fredriknk/spimux/CAD/Relay_group.kicad_sch

## KiCad design CAD/Relay_group.kicad_sch (2023-02-07)

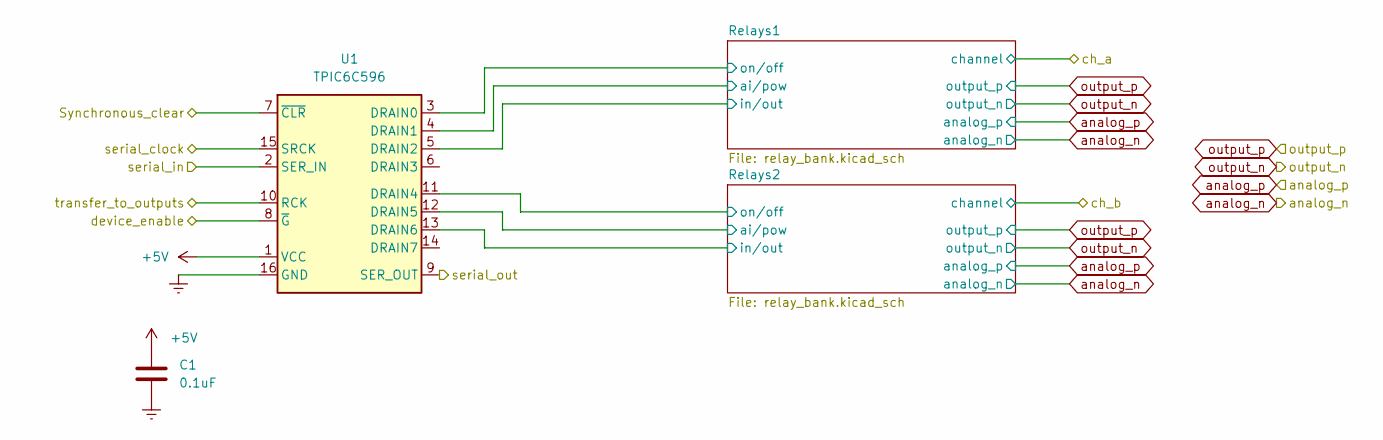
[picture p32: schematic Relay_group.kicad_sch]

Parts:
C1: 0.1uF; D_0603_1608Metric; Digikey CL10B104KB8NFNC
U1: TPIC6C596; TSSOP-16_4.4x5mm_P0.65mm; Digikey TPIC6C596PWR

Connections:
+5V: C1.1, U1.1 (VCC)
Earth: C1.2, U1.16 (GND)
Synchronous_clear: U1.7 (~CLR)
ai/pow: U1.4 (DRAIN1), U1.12 (DRAIN5)
device_enable: U1.8 (~G)
in/out: U1.5 (DRAIN2), U1.13 (DRAIN6)
on/off: U1.3 (DRAIN0), U1.11 (DRAIN4)
serial_clock: U1.15 (SRCK)
serial_in: U1.2 (SER_IN)
serial_out: U1.9 (SER_OUT)
transfer_to_outputs: U1.10 (RCK)
