fredriknk/spimux/CAD/buffer.kicad_sch

## KiCad design CAD/buffer.kicad_sch (2023-02-07)

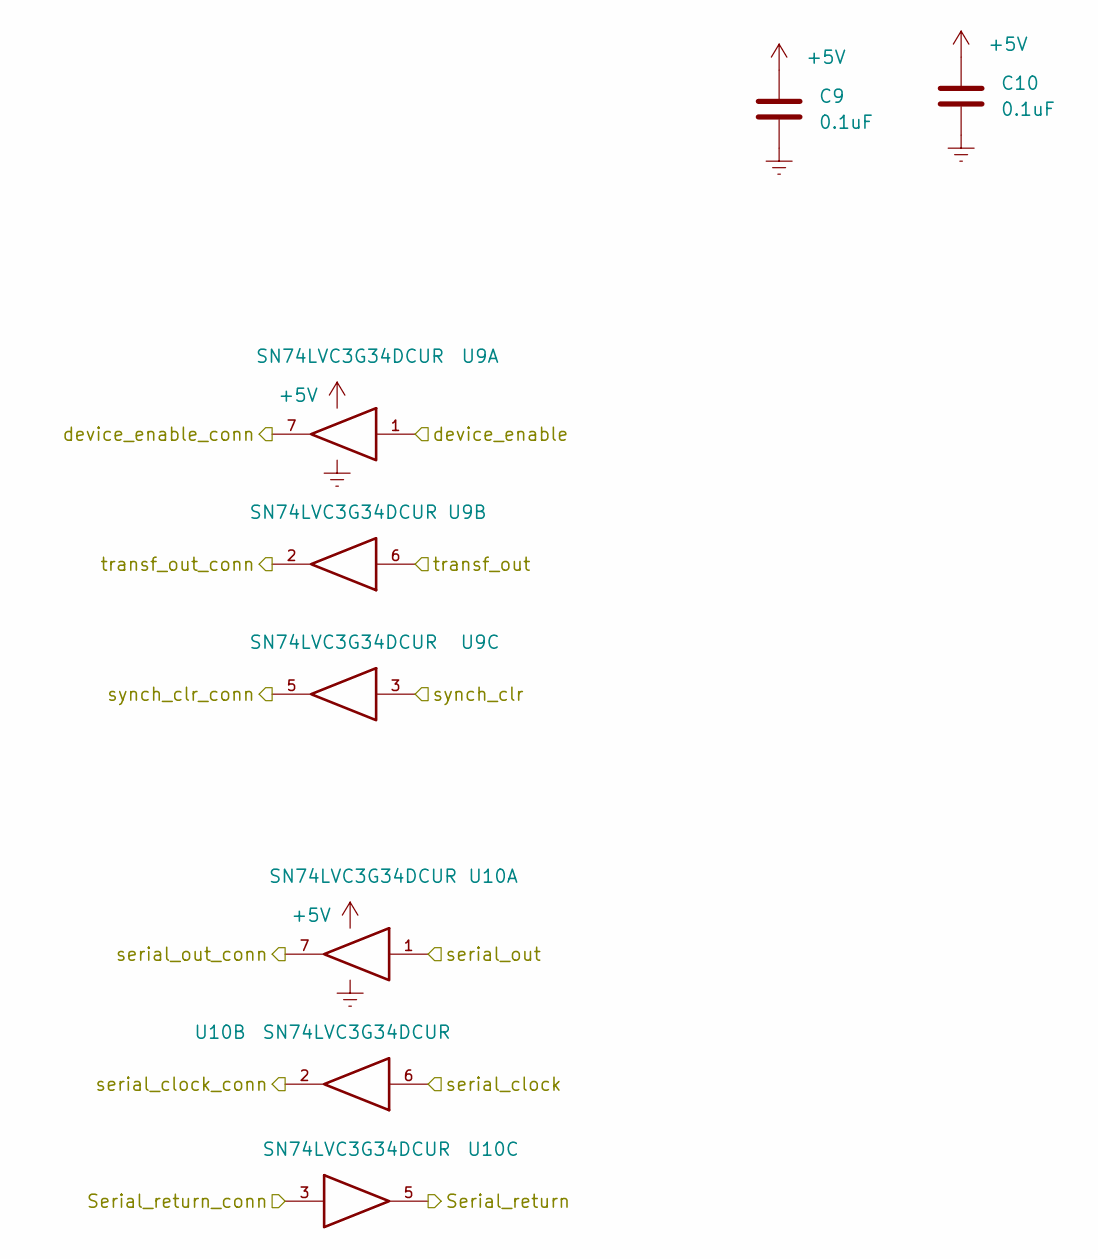
[picture p33: schematic buffer.kicad_sch]

Parts:
C9, C10: 0.1uF; D_0603_1608Metric; Digikey CL10B104KB8NFNC
U9, U10: SN74LVC3G34DCUR; VSSOP-8_2.3x2mm_P0.5mm; Digikey SN74LVC3G34DCUR

Connections:
+5V: C9.1, C10.1, U9.8 (VCC), U10.8 (VCC)
Earth: C9.2, C10.2, U9.4 (GND), U10.4 (GND)
Serial_return: U10.5
Serial_return_conn: U10.3
device_enable: U9.1
device_enable_conn: U9.7
serial_clock: U10.6
serial_clock_conn: U10.2
serial_out: U10.1
serial_out_conn: U10.7
synch_clr: U9.3
synch_clr_conn: U9.5
transf_out: U9.6
transf_out_conn: U9.2
