fredriknk/spimux/CAD/eurocard mux.kicad_sch

## KiCad design CAD/eurocard mux.kicad_sch (2023-02-07)

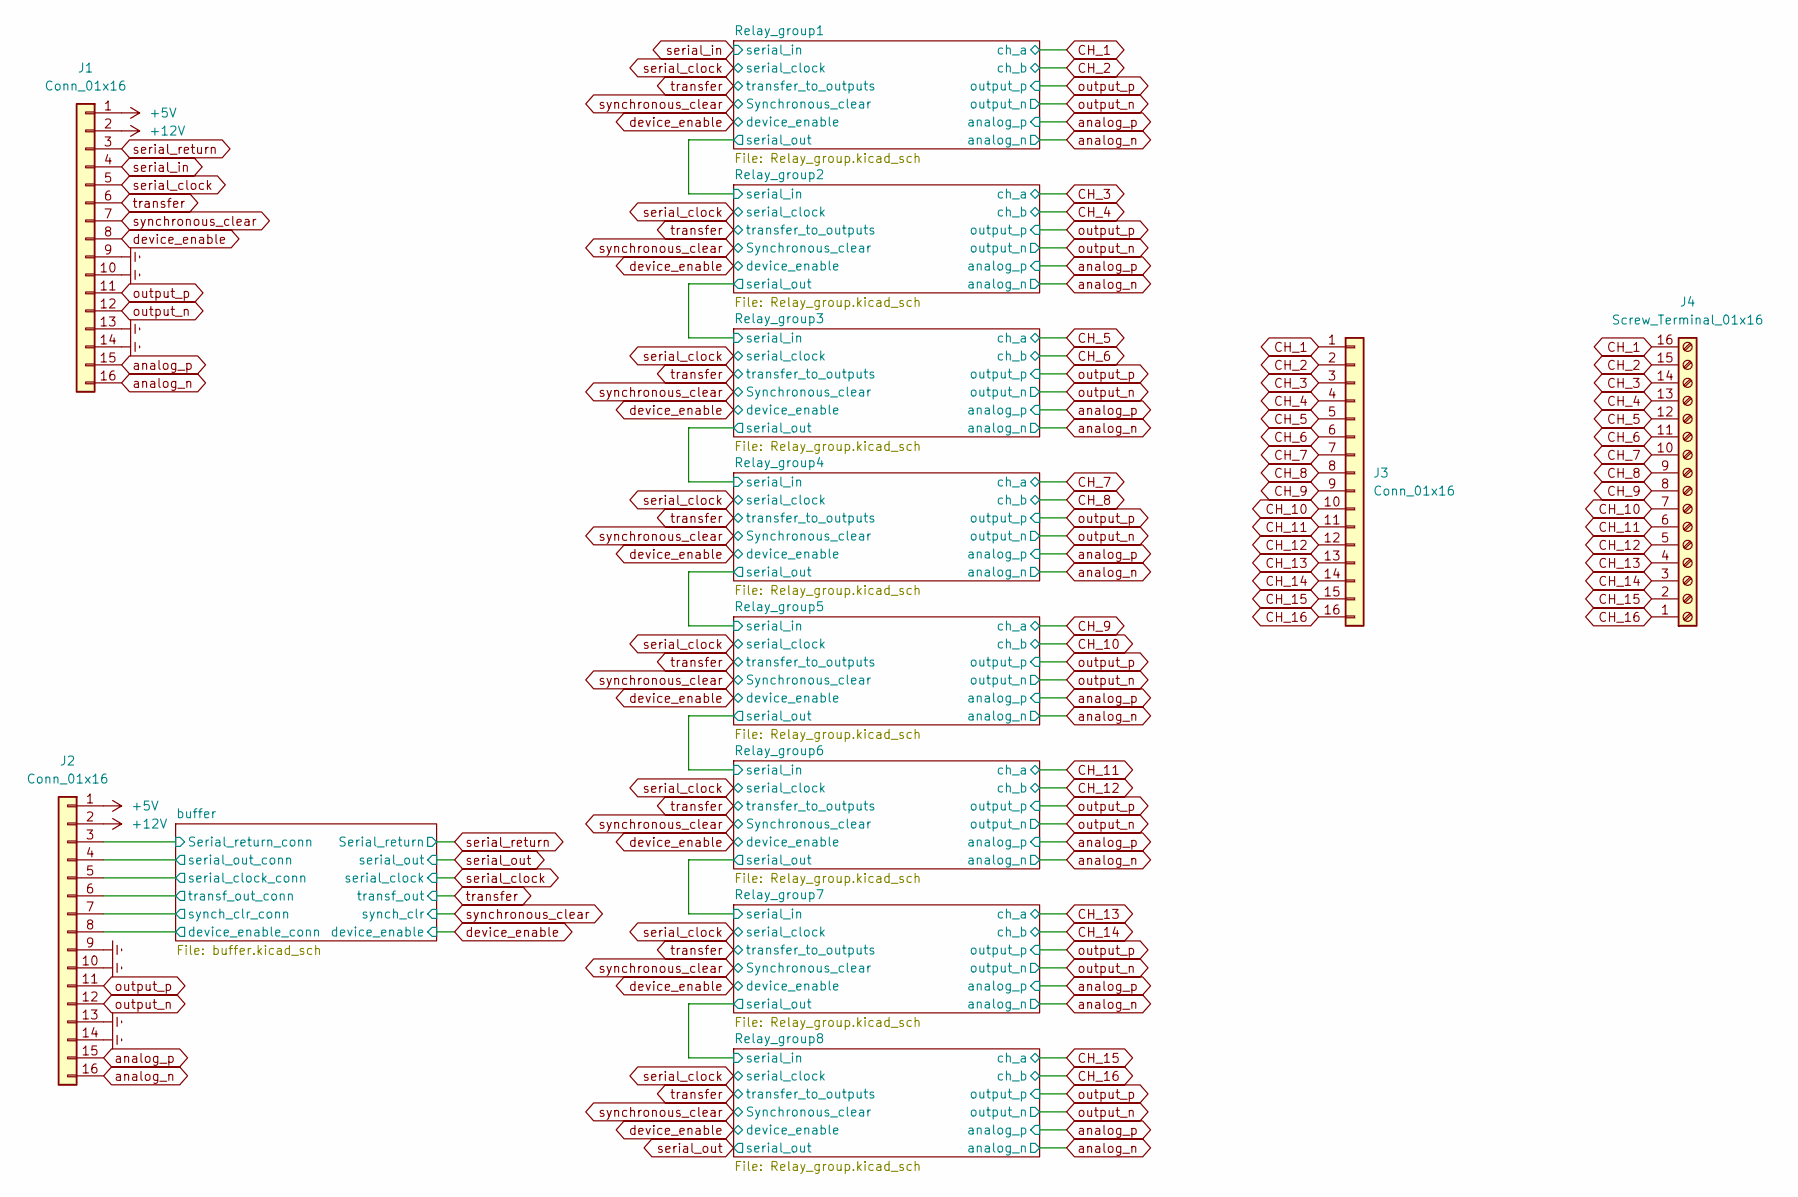
[picture p34: schematic eurocard mux.kicad_sch]

Parts:
J1, J2: Conn_01x16; IDC-Header_2x08_P2.54mm_Horizontal; Digikey 3020-16-0200-00
J3: Conn_01x16; IDC-Header_2x08_P2.54mm_Vertical; Digikey 3020-16-0200-00
J4: Screw_Terminal_01x16; TerminalBlock_Phoenix_MKDS-1,5-16_1x16_P5.00mm_Horizontal; Digikey TB003-500-P16BE

Connections:
+5V: J1.1, J2.1
+12V: J1.2, J2.2
CH_1: J3.1, J4.16
CH_2: J3.2, J4.15
CH_3: J3.3, J4.14
CH_4: J3.4, J4.13
CH_5: J3.5, J4.12
CH_6: J3.6, J4.11
CH_7: J3.7, J4.10
CH_8: J3.8, J4.9
CH_9: J3.9, J4.8
CH_10: J3.10, J4.7
CH_11: J3.11, J4.6
CH_12: J3.12, J4.5
CH_13: J3.13, J4.4
CH_14: J3.14, J4.3
CH_15: J3.15, J4.2
CH_16: J3.16, J4.1
Earth: J1.9, J1.10, J1.13, J1.14, J2.9, J2.10, J2.13, J2.14
Serial_return_conn: J2.3
analog_n: J1.16, J2.16
analog_p: J1.15, J2.15
device_enable: J1.8
device_enable_conn: J2.8
output_n: J1.12, J2.12
output_p: J1.11, J2.11
serial_clock: J1.5
serial_clock_conn: J2.5
serial_in: J1.4
serial_out_conn: J2.4
serial_return: J1.3
synch_clr_conn: J2.7
synchronous_clear: J1.7
transf_out_conn: J2.6
transfer: J1.6
