fredriknk/spimux/CAD/relay_bank.kicad_sch

## KiCad design CAD/relay_bank.kicad_sch (2023-02-07)

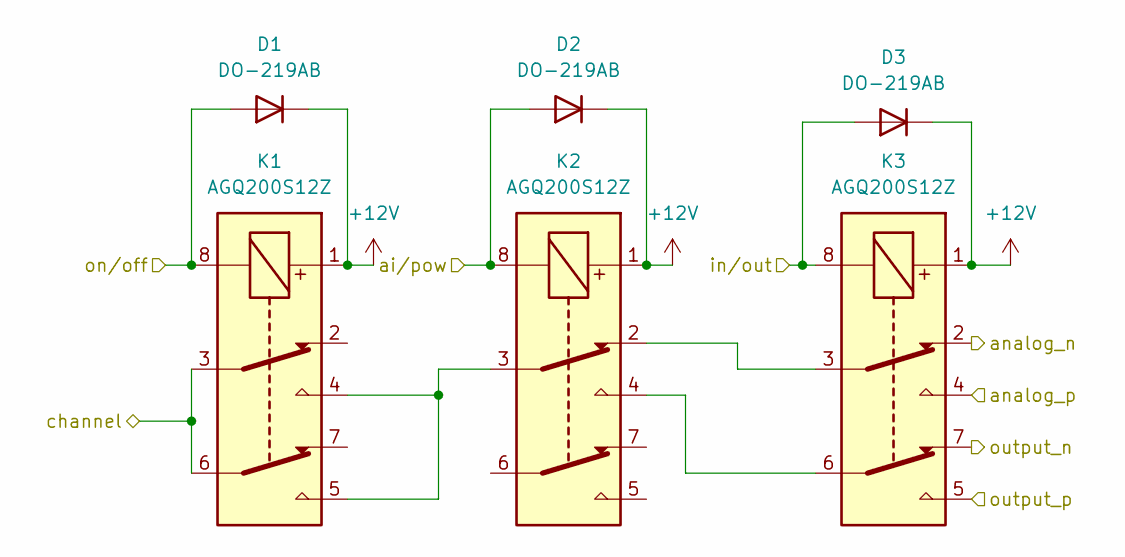
[picture p35: schematic relay_bank.kicad_sch]

Parts:
D1, D2, D3: DO-219AB; D_SMF; Digikey S1FLM-GS18
K1, K2, K3: AGQ200S12Z; Relay_2P2T_10x6mm_TE_IMxxG; Digikey AGQ200S12Z

Connections:
+12V: D1.1 (K), D2.1 (K), D3.1 (K), K1.1, K2.1, K3.1
unnamed: K1.4, K1.5, K2.3
unnamed: K2.2, K3.3
unnamed: K2.4, K3.6
ai/pow: D2.2 (A), K2.8
analog_n: K3.2
analog_p: K3.4
channel: K1.3, K1.6
in/out: D3.2 (A), K3.8
on/off: D1.2 (A), K1.8
output_n: K3.7
output_p: K3.5
